dodohand/dodohand/3D_models/show_carrier.scad

use <carrier.scad>;
use <5key_assy.scad>;


include <dimensions.scad>;


carrier_group(0, 0, 0, 0, 0, 0, 0, 0, 0, 0);
