dodohand/dodohand/src/n35p112.c

/*
    This file is part of the DodoHand project. This project aims to create 
    an open implementation of the DataHand keyboard, capable of being created
    with commercial 3D printing services.

    Copyright (C) 2013 Scott Fohey

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
    You should have received a copy of the GNU General Public License
    along with this program.  If not, see <http://www.gnu.org/licenses/>.
*/


#include "n35p112.h"



/*
 * Define the I2C command sequences for initialization and for reading
 *
 * Initalialization first:
 *
 * Datasheet says after power-on, a reset is required for >100ns.
 * Then loop on register 0x0F until 0xF0 or 0xF1 is present.
 * Then write 0x06h to register 0x2D (TCR)
 */


#define N35P112_W4RDY_CMD_CNT ( 7u )
t_dh_twi_cmd n35p112_w4rdy_cmds[N35P112_W4RDY_CMD_CNT] = {
  { DH_TWI_CMD_START, 0 },
  { 0, EASYPOINT_I2C_ADDR | TW_WRITE },
  { 0, N35P112_CR1_ADDR },
  { DH_TWI_CMD_START, 0 },
  { 0, EASYPOINT_I2C_ADDR | TW_READ },
  { DH_TWI_CMD_READ, 0 }, // elicit value of CR1
  { DH_TWI_CMD_STOP, 0 }
};

static t_dh_twi_packet w4rdy_pkt = { N35P112_W4RDY_CMD_CNT,
                                     0,
                                     0,
                                     n35p112_w4rdy_cmds };

#define N35P112_W4RDY_GET_CR1 ( n35p112_w4rdy_cmds[5].dat )

#define N35P112_RDPOS_CMD_CNT ( 9u )
t_dh_twi_cmd n35p112_rdpos_cmds[N35P112_RDPOS_CMD_CNT] = {
  { DH_TWI_CMD_START, 0 },
  { 0, EASYPOINT_I2C_ADDR | TW_WRITE },
  { 0, N35P112_CR1_ADDR },
  { DH_TWI_CMD_START, 0 },
  { 0, EASYPOINT_I2C_ADDR | TW_READ },
  { DH_TWI_CMD_READ | DH_TWI_CMD_ACK, 0 }, // elicit value of CR1
  { DH_TWI_CMD_READ | DH_TWI_CMD_ACK, 0 }, // elicit value of XR
  { DH_TWI_CMD_READ, 0 },                  // elicit value of YR
  { DH_TWI_CMD_STOP, 0 }
};

static t_dh_twi_packet rdpos_pkt = { N35P112_RDPOS_CMD_CNT,
                                     0,
                                     0,
                                     n35p112_rdpos_cmds };

#define N35P112_RDPOS_GET_CR1 ( n35p112_rdpos_cmds[5].dat )
#define N35P112_RDPOS_GET_XR ( n35p112_rdpos_cmds[6].dat )
#define N35P112_RDPOS_GET_YR ( n35p112_rdpos_cmds[7].dat )


#define N35P112_INIT_CMD_CNT ( 8u )
const t_dh_twi_cmd n35p112_init_cmds[N35P112_INIT_CMD_CNT] = {
  { DH_TWI_CMD_START, 0 },
  { 0, EASYPOINT_I2C_ADDR | TW_WRITE },
  { 0, N35P112_MCR_ADDR },
  { 0, 0 }, // MCR must be set to zero after power-up
  { 0, 0x06u }, // JCR must be set to 0x06 after power-up
  { 0, 0x06u }, // tcr must be set to 0x06 after power-up
  { 0, 0x86u }, // CR2 must be set to 0x86 for easpoint module  
  { DH_TWI_CMD_STOP, 0 }
};

static t_dh_twi_packed init_pkt = { N35P112_INIT_CMD_CNT,
                                    0,
                                    0,
                                    n35p112_init_cmds };
